alrapal/Greeny/MicroPython/change_my_secrets.py

secrets = {
   'ssid' : '',
   'password' : ''
   }

mqtt_credentials = {
    'username':'',
    'key':''
}

mqtt_feeds = {
    'ambient_temperature':'greeny/feeds/temperature',
    'ambient_humidity':'greeny/feeds/ambient-humidity',
    'ambient_light':'greeny/feeds/ambient-light',
    'soil_moisture': 'greeny/feeds/soil-moisture',
    'device_monitoring':'greeny/feeds/monitoring'
}
