alrapal/Greeny/MicroPython/WIFI.py

# Modified version of the original code: https://hackmd.io/@lnu-iot/rJVQizwUh from @author: LNU Applied IoT
# Modified to be an object and include a disconnect method as well as some attributes 

import network
from time import sleep
from my_secrets import secrets  # secrets is not pushed to avoid having WIFI access on github

class WifiConnector():

    wlan: network.WLAN
    debug: bool
    ip: str
    def __init__(self, debug: bool = False) -> None:
        self.wlan = network.WLAN(network.STA_IF)  
        self.debug = debug
        self.ip = ""

    def is_connected(self) -> bool:
       return self.wlan.isconnected()

    def do_connect(self):
        if not self.is_connected():                       # Check if already connected
            if self.debug:
                print('connecting to network...')
            self.wlan.active(True)                       # Activate network interface
            # set power mode to get WiFi power-saving off (if needed)
            self.wlan.config(pm = 0xa11140)
            self.wlan.connect(secrets["ssid"], secrets["password"])  # Your WiFi Credential
            if self.debug:
                print('Waiting for connection...', end='')
            # Check if it is connected otherwise wait
            while not self.is_connected() and self.wlan.status() >= 0:
                print('.', end='')
                sleep(1)
        # Print the IP assigned by router
        self.ip = self.wlan.ifconfig()[0]
        if self.debug:
            print('\nConnected on {}'.format(self.ip))
        return self.ip 


    def http_get(self, url = 'http://detectportal.firefox.com/'):
        import socket                           # Used by HTML get request
        import time                             # Used for delay
        _, _, host, path = url.split('/', 3)    # Separate URL request
        addr = socket.getaddrinfo(host, 80)[0][-1]  # Get IP address of host
        s = socket.socket()                     # Initialise the socket
        s.connect(addr)                         # Try connecting to host address
        # Send HTTP request to the host with specific path
        s.send(bytes('GET /%s HTTP/1.0\r\nHost: %s\r\n\r\n' % (path, host), 'utf8'))    
        time.sleep(1)                           # Sleep for a second
        rec_bytes = s.recv(10000)               # Receve response
        print(rec_bytes)                        # Print the response
        s.close()                               # Close connection

    def disconnect(self) -> None: 
        self.wlan.disconnect()
        if self.debug:
            print("Disconnecting from {}".format(self.ip))

    def get_ip(self) -> str:
        return self.ip
